nickbild/sonicsight_ar/media/case.jpg

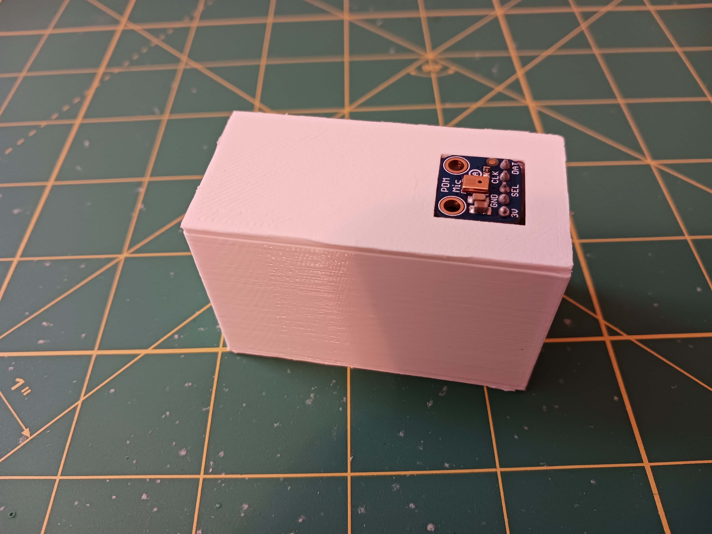
media/case.jpg
