nickbild/sonicsight_ar/media/photon.jpg

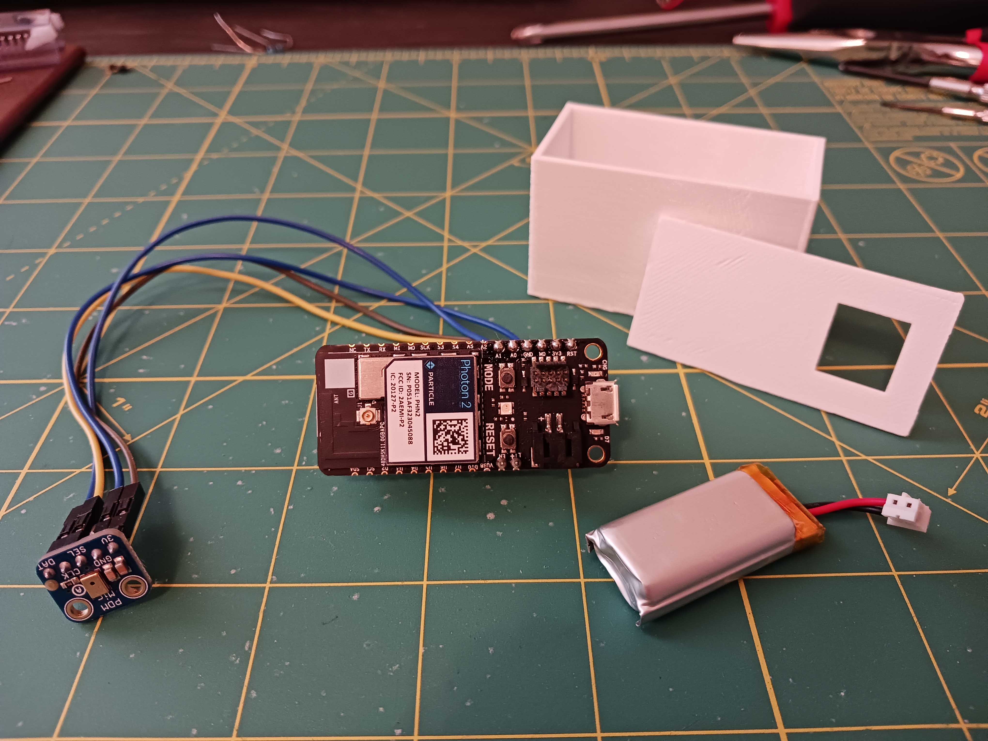
media/photon.jpg
